ramonimbao/kusuguru/firmware/matrix.c

/*
Copyright 2012-2018 Jun Wako, Jack Humbert, Yiancar

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
You should have received a copy of the GNU General Public License
along with this program.  If not, see <http://www.gnu.org/licenses/>.
*/
#include <stdint.h>
#include <stdbool.h>
#include "wait.h"
#include "print.h"
#include "debug.h"
#include "util.h"
#include "matrix.h"
#include "debounce.h"
#include "quantum.h"

static const pin_t row_pins[MATRIX_ROWS] = MATRIX_ROW_PINS;
static const pin_t col_pins[MATRIX_COLS] = MATRIX_COL_PINS;

static matrix_row_t raw_matrix[MATRIX_ROWS];  // raw values
static matrix_row_t matrix[MATRIX_ROWS];      // debounced values

__attribute__((weak)) void matrix_init_quantum(void) { matrix_init_kb(); }

__attribute__((weak)) void matrix_scan_quantum(void) { matrix_scan_kb(); }

__attribute__((weak)) void matrix_init_kb(void) { matrix_init_user(); }

__attribute__((weak)) void matrix_scan_kb(void) { matrix_scan_user(); }

__attribute__((weak)) void matrix_init_user(void) {}

__attribute__((weak)) void matrix_scan_user(void) {}

#define print_matrix_header() print("\nr/c 0123456789ABCDEF\n")
#define print_matrix_row(row) print_bin_reverse16(matrix_get_row(row))
#define matrix_bitpop(i) bitpop16(matrix[i])

void matrix_print(void) {
    print_matrix_header();

    for (uint8_t row = 0; row < MATRIX_ROWS; row++) {
        phex(row);
        print(": ");
        print_matrix_row(row);
        print("\n");
    }
}

inline matrix_row_t matrix_get_row(uint8_t row) {
    return matrix[row];
}

static void select_col(uint8_t col) {
    setPinOutput(col_pins[col]);
    writePinLow(col_pins[col]);
}

static void unselect_col(uint8_t col) { setPinInputHigh(col_pins[col]); }

static void unselect_cols(void) {
    for (uint8_t x = 0; x < MATRIX_COLS; x++) {
        setPinInputHigh(col_pins[x]);
    }
}

static void init_pins(void) {
    unselect_cols();
    for (uint8_t x = 0; x < MATRIX_ROWS; x++) {
        setPinInputHigh(row_pins[x]);
    }
}

static bool read_rows_on_col(matrix_row_t current_matrix[], uint8_t current_col) {
    bool matrix_changed = false;

    // Select col and wait for col selecton to stabilize
    select_col(current_col);
    wait_us(30);

    // For each row...
    for (uint8_t row_index = 0; row_index < MATRIX_ROWS; row_index++) {
        // Store last value of row prior to reading
        matrix_row_t last_row_value = current_matrix[row_index];

        // Check row pin state
        if (readPin(row_pins[row_index]) == 0) {
            // Pin LO, set col bit
            current_matrix[row_index] |= ((uint16_t)1 << current_col);
        } else {
            // Pin HI, clear col bit
            current_matrix[row_index] &= ~((uint16_t)1 << current_col);
        }

        // Determine if the matrix changed state
        if ((last_row_value != current_matrix[row_index]) && !(matrix_changed)) {
            matrix_changed = true;
        }
    }

    // Unselect col
    unselect_col(current_col);

    return matrix_changed;
}

void matrix_init(void) {
    // initialize key pins
    init_pins();

    // initialize matrix state: all keys off
    for (uint8_t i = 0; i < MATRIX_ROWS; i++) {
        raw_matrix[i] = 0;
        matrix[i]     = 0;
    }

    debounce_init(MATRIX_ROWS);

    matrix_init_quantum();
}

uint8_t matrix_scan(void) {
    bool changed = false;

    // Set col, read rows
    for (uint8_t current_col = 0; current_col < MATRIX_COLS; current_col++) {
        changed |= read_rows_on_col(raw_matrix, current_col);
    }

    debounce(raw_matrix, matrix, MATRIX_ROWS, changed);

    matrix_scan_quantum();
    return (uint8_t)changed;
}
